GR3Y-SCALE/EGB220-A10/firmware/line-follower/arduino/V2/Line_Following_2.1/PIDMotorControl.h

// PID constants
extern float Kp;   
extern float Ki; 
extern float Kd;   

// Variables for PID
extern float previousError;
extern float integral; 

void PIDMotorControl();

void stopMotors();

extern int lap;
extern bool SZ;
